PHAP0610/NHAP/Code/TestSTM32/Core/Inc/7seg.h

/*
 * 7seg.h
 *
 *  Created on: Jul 5, 2023
 *      Author: KHOA
 */

#ifndef INC_7SEG_H_
#define INC_7SEG_H_

#include "main.h"

#define LE3_BIT 8
#define LE2_BIT 9
#define LE1_BIT 10

void SegLed_TestAllOutput();
void SegLed_OutputDigit();
#endif /* INC_7SEG_H_ */
