PHAP0610/NHAP/Code/TestSTM32/Core/Inc/Buzzer.h

/*
 * Buzzer.h
 *
 *  Created on: Jul 5, 2023
 *      Author: VTP
 */

#ifndef _INC_BUZZER_H_
#define _INC_BUZZER_H_
#include "main.h"

void BuzzerOnOff(int delayOn, int delayOff);
void BuzzerToggle();
void BuzzerOn(int On);
void BuzzerOff(int Off);
#endif
